P90Ez/DIYTagConnect/Pictures/26-05-14 20-16-57 2749.jpg

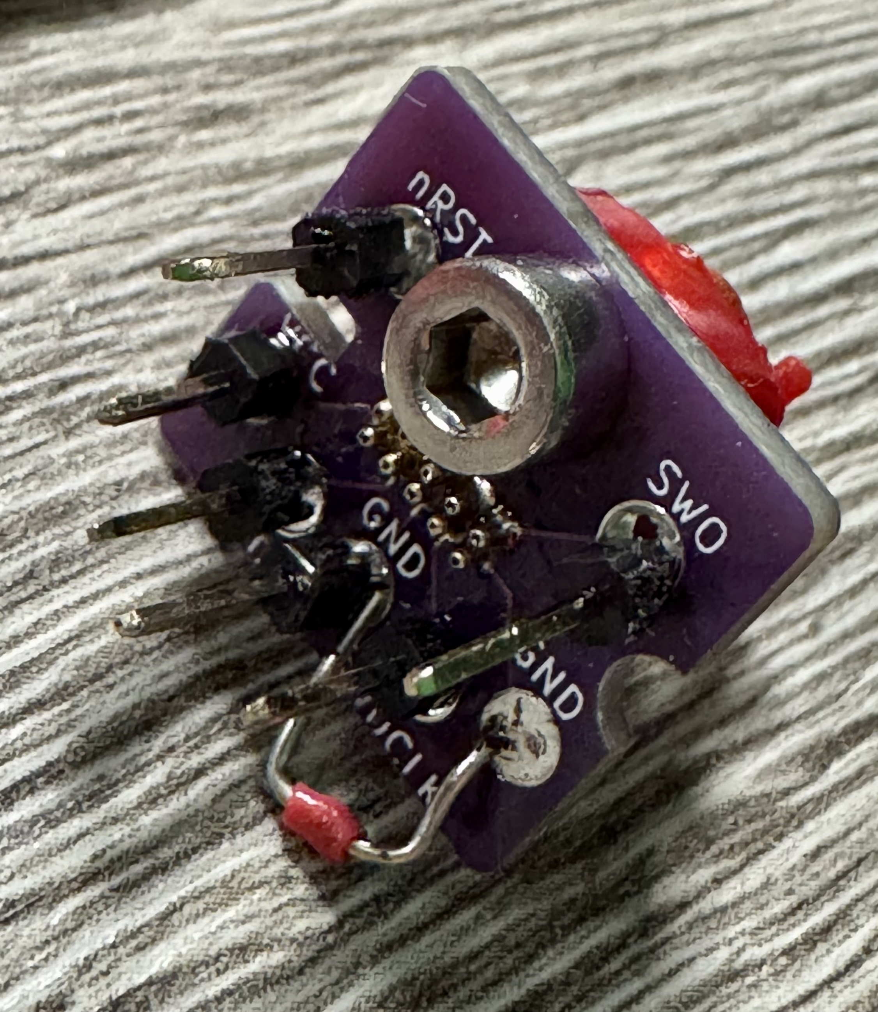
Pictures/26-05-14 20-16-57 2749.jpg
